aeonSolutions/AeonLabs-MCU-Burner-USB-to-UART-TTL/designs/pcb.fw.png

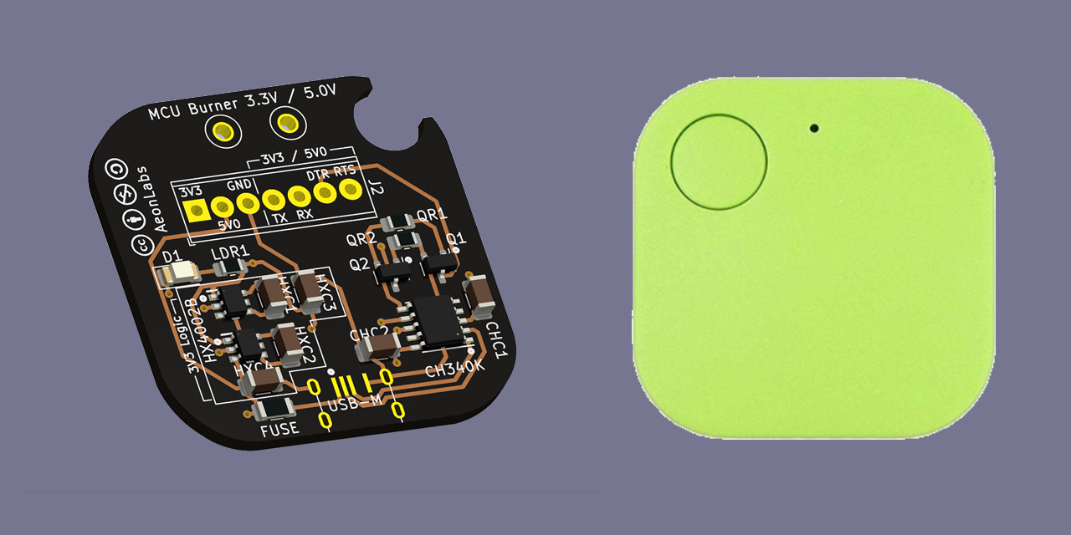
designs/pcb.fw.png
